vdbvincent/catfeeder/src/common.h

/*
 * common.h
 *
 *  Created on: 31 juil. 2015
 *      Author: vincent
 */

#ifndef _COMMON_H_
#define _COMMON_H_

#include <stdio.h>
#include <stdlib.h>

// Définitions des modes de debug
//#define MDEBUG  // logs moteur
#define BDEBUG  // logs boutons
//#define MANDEBUG  // logs du manager
//#define CDEBUG  // logs clock
//#define ADEBUG  // logs alarme
#define MEDEBUG // logs menu

/* Définition des événements */
#define NO_EVENT    -1
// Définition des événements boutons
#define NON_PRESSE  0
#define ENFONCE     1
#define PRESSE      2

#define AUCUN_EVENEMENT   0
#define EVENEMENT_PRESSE  1
#define EVENEMENT_RELACHE 2

#define BT_G_PRESSE  0
#define BT_G_RELACHE 1
#define BT_D_PRESSE  2
#define BT_D_RELACHE 3
#define BT_H_PRESSE  4
#define BT_H_RELACHE 5
#define BT_B_PRESSE  6
#define BT_B_RELACHE 7

#define BOUTON_HAUT   0
#define BOUTON_BAS    1
#define BOUTON_GAUCHE 2
#define BOUTON_DROIT  3
#define BOUTOU_NONE   4

// Définition des événements moteur
#define FEDD1  1
#define FEED2  2
#define FEED3  3
#define BEGIN  4
#define END    5

// Définition des criticité des logs
#define ERREUR 1
#define INFO   2
#define DEBUG  3


/* Définition du type bool */
typedef enum 
{ False = 0, True = 1}
Bool;

/* Définition de la structure clock */
typedef struct
{
  uint8_t heures;
  uint8_t minutes;
  uint8_t secondes;
}clock;


#endif /* _COMMON_H_ */
